pyroesp/GBDSO/pictures/bottom - out.png

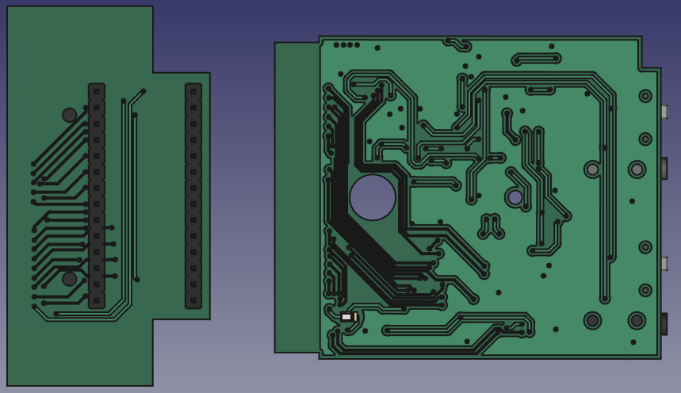
pictures/bottom - out.png
