pyroesp/GBDSO/pictures/original/GBDSO_B.jpg

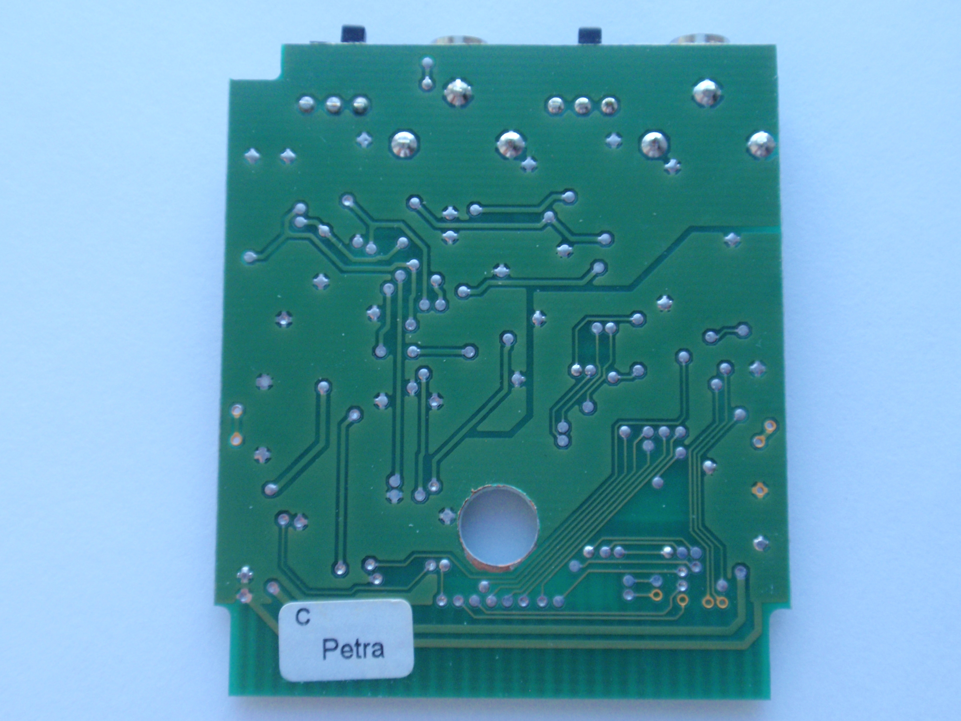
pictures/original/GBDSO_B.jpg
