pyroesp/GBDSO/pictures/pcb-v1-back.jpg

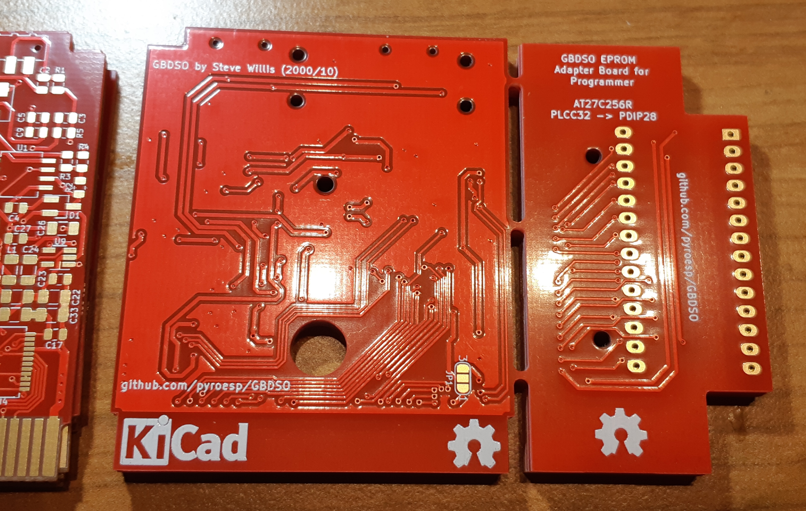
pictures/pcb-v1-back.jpg
