pyroesp/GBDSO/pictures/side - in.png

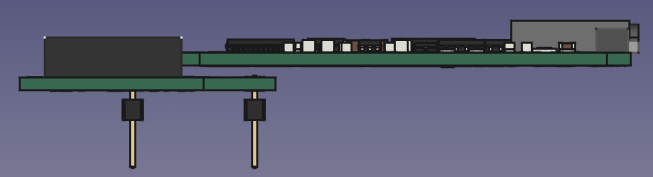
pictures/side - in.png
